isairey/RadarDeteccionObjetos/5_Simulations/array_pattern_heatmap.png

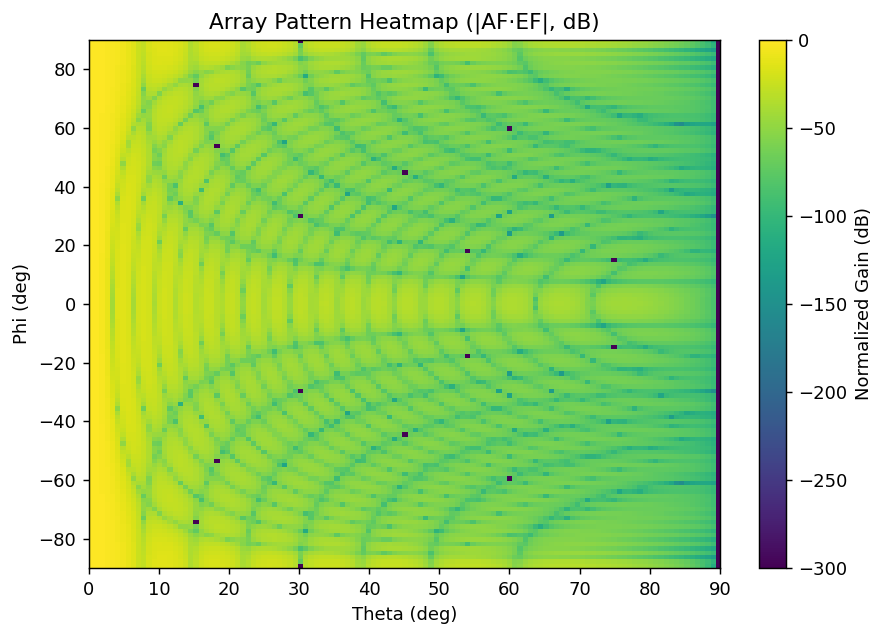
5_Simulations/array_pattern_heatmap.png
