isairey/RadarDeteccionObjetos/5_Simulations/E_plane_cut.png

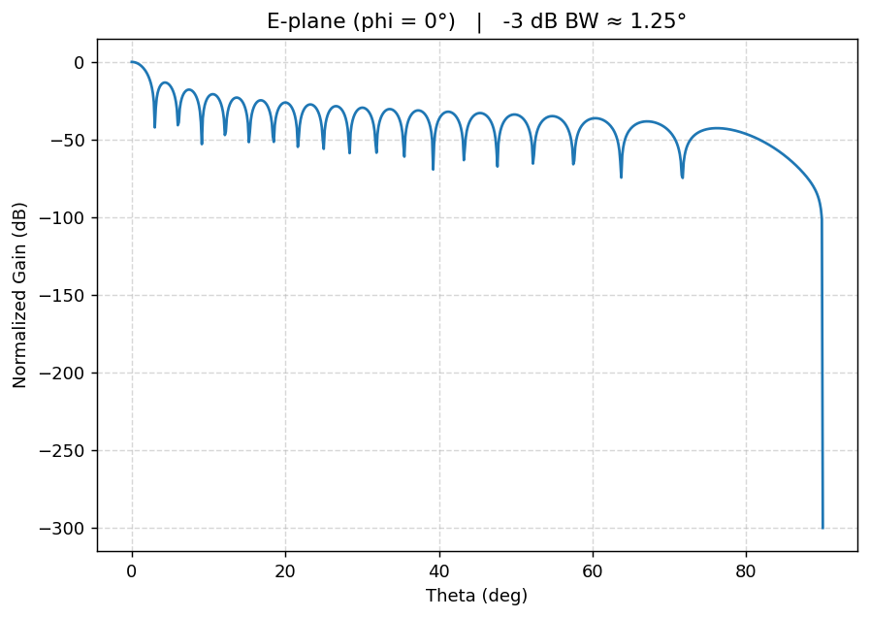
5_Simulations/E_plane_cut.png
