isairey/RadarDeteccionObjetos/5_Simulations/E_plane_Kaiser25dB_like.png

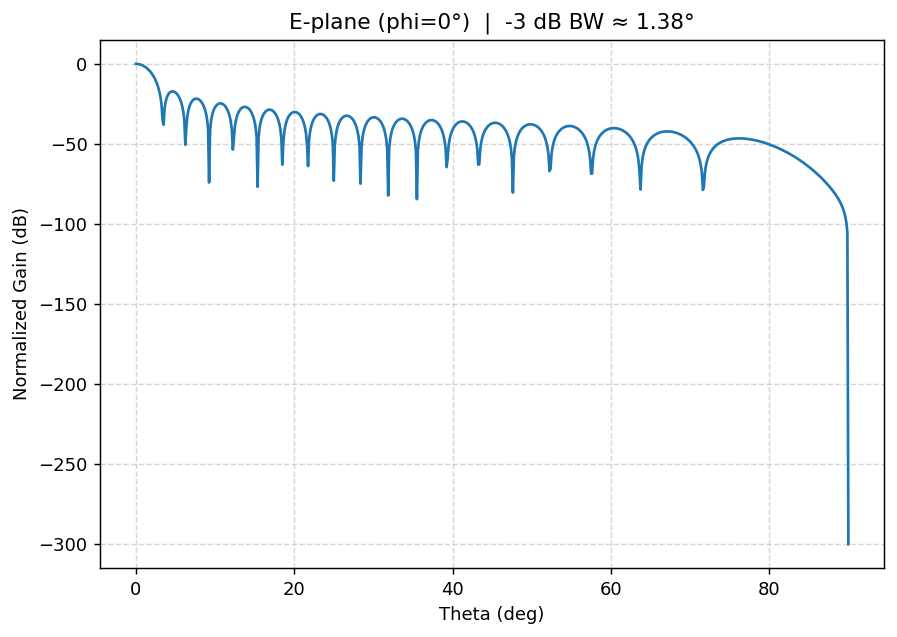
5_Simulations/E_plane_Kaiser25dB_like.png
