isairey/RadarDeteccionObjetos/5_Simulations/H_plane_cut.png

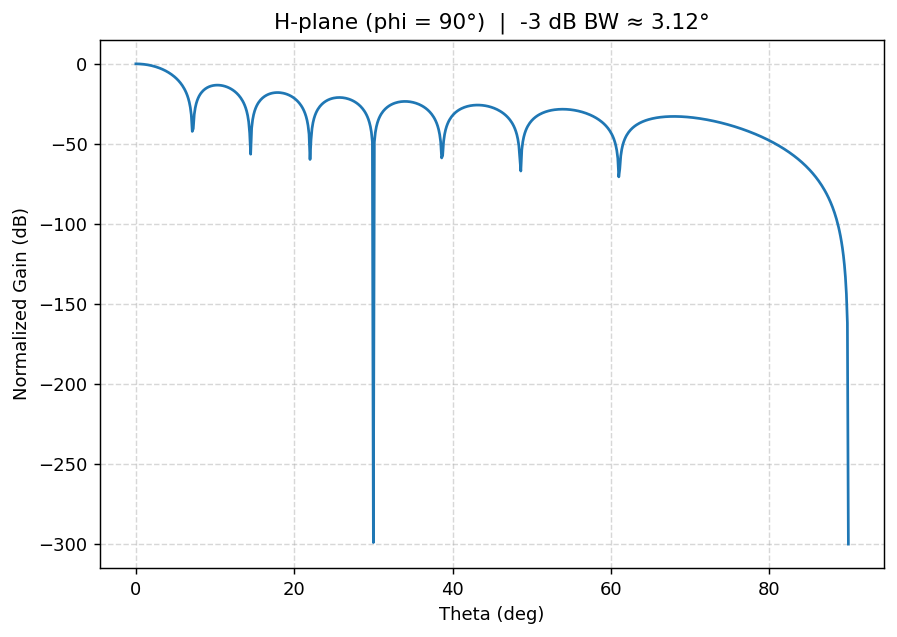
5_Simulations/H_plane_cut.png
