isairey/RadarDeteccionObjetos/8_Utils/AERIS-10_RADAR.png

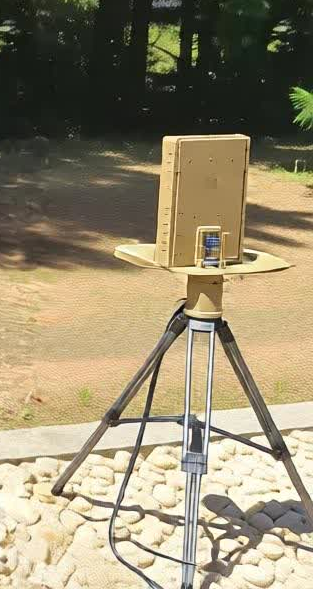
8_Utils/AERIS-10_RADAR.png
