isairey/RadarDeteccionObjetos/8_Utils/b79a6fe3-5abf-473d-b3e2-178e6a9cf4da - Copie.jpg

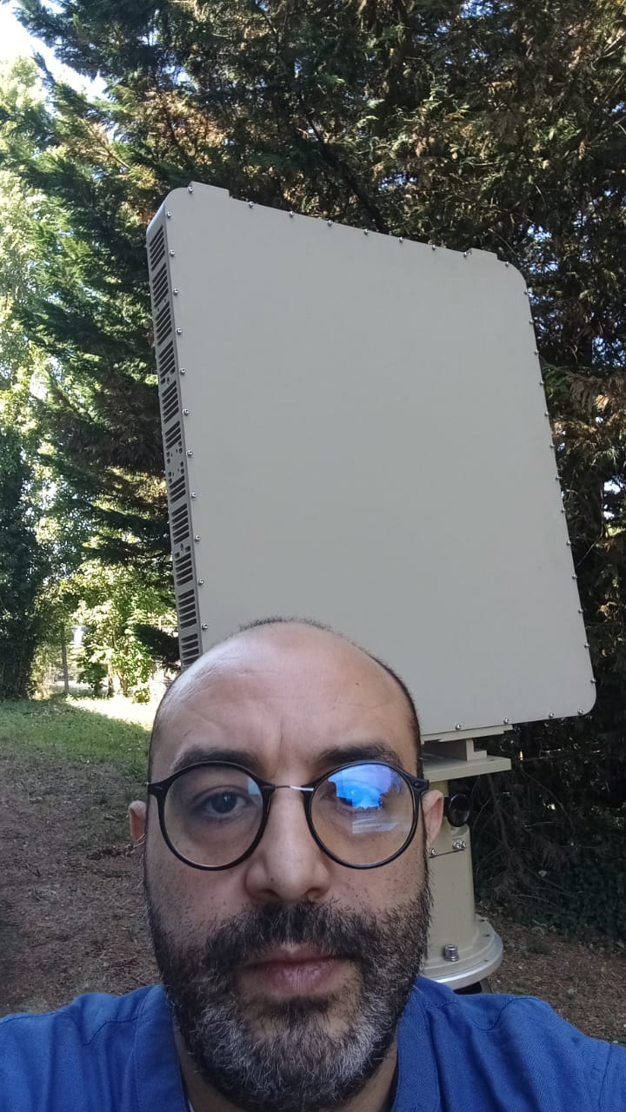
8_Utils/b79a6fe3-5abf-473d-b3e2-178e6a9cf4da - Copie.jpg
