isairey/RadarDeteccionObjetos/8_Utils/Nawfal.png

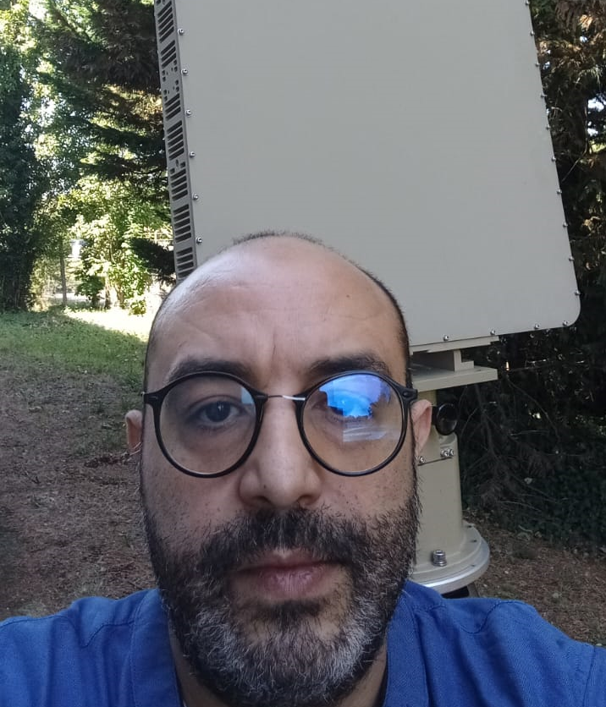
8_Utils/Nawfal.png
