isairey/RadarDeteccionObjetos/8_Utils/PCBWAY.jpg

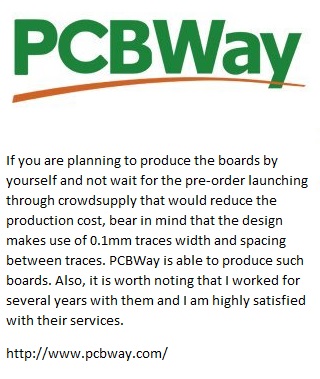
8_Utils/PCBWAY.jpg
