isairey/RadarDeteccionObjetos/3_Power Management/Power Management V6.xlsx

BOARD | COMPONENT | PART NUMBER | N° | VOLTAGE PINS | RATING (V) | CURRENT (mA) | SELECTED VOLTAGE (V) | VOLTAGE RAIL | VOLTAGE RAIL AFTER BRANCHING AND FILTERING | ENABLE V | SEQUENCE
CLOCKS & FREQUENCY SYNTHESIZER BOARD | OCXO | ECOC-2522-100.000-3FC | 1 | VDD | [3,135-3,465] | 1200 | 3.3 | +3V3_XO |  | NO | NO
 |  |  |  | VREF |  |  | 3,3/2 | +3V3_XO |  | NO | NO
 | XO | CCHD-957-100 | 1 | VDD | [3-3,6] | 25 | 3.3 | +3V3_XO |  | NO | NO
 | VCXO | CVHD-950-100.000 | 1 | VDD | [3-3,6] | 25 | 3.3 | +3V3_XO |  | NO | NO
 | CLOCK SYNTHESIZER | AD9523 | 1 | VDD3_REF, VDD3_PLL, VDD3_OUT | 3.3 | 250 | 3.3 | +3V3_CLOCK |  | YES | bring the 1.8 V supplies high and stable prior to or simultaneously with the 3.3 V supplies. It is recommended to hold the RESET pin low while both supply domains settle to ensure that the 3.3 V supplies do not lead the 1.8 V supplies
 |  |  |  | VDD1.8_OUT | 1.8 | 250 | 1.8 | +1V8_CLOCK |  | YES
 | LO | ADF4382 | 2 | V5_VCO | [4,75-5,25] | 200 | 5 | +5V0_LO |  | NO | NO
 |  |  |  | V5_CAL | [4,75-5,25] | 0.3 | 5 | +5V0_LO |  | NO | NO
 |  |  |  | V5_CP | [4,75-5,25] | 70 | 5 | +5V0_LO |  | NO | NO
 |  |  |  | V3V3_1 | [3,15-3,45] | 240 | 3.3 | +3V3_LO_1 |  | NO | NO
 |  |  |  | V3V3_2 | [3,15-3,45] | 340 | 3.3 | +3V3_LO_2 |  | NO | NO
MAIN BOARD | MICROCONTROLLER | STM32F746ZGT7 | 1 | VCC | 3.3 | 130 | 3.3 | +3V3 |  | NO | NO
 | FPGA | XC7A50T-2FTG256 | 1 | VCC0_BANK | 1.8 | 50 | 1.8 | +1V8_FPGA |  | YES
 |  |  |  | VCCO_O | 3.3 | 20 | 3.3 | +3V3_FPGA |  | YES | +1V0_FPGA
 |  |  |  | VCCBAT, VCCADC, VCCAUX | 1.8 | 22 | 1.8 | +1V8_FPGA |  | YES | +1V8_FPGA
 |  |  |  | VCCBRAM, VCCINT | 1 | 30 | 1 | +1V0_FPGA |  | YES | +3V3_FPGA
 |  |  |  | VCCO_BANK x 3 | 3.3 | 200 | 3.3 | +3V3_FPGA |  | YES
 | DAC | AD9708 | 1 | AVDD | [2,7-5,5] | 30 | 3.3 | +3V3_AN | +3V3_AN | NO | NO
 |  |  |  | DVDD | [2,7-5,5] | 20 | 3.3 | +3V3_FPGA |  | NO | NO
 | Mixer | LTC5552 | 2 | VCC | [3,0-3,6] | 150 | 3.3 | +3V3_AN | +3V3_AN1_F |+3V3_AN2_F | NO | NO
 | RF SWITCH | M3SWA2-34DR+ | 17 | VDD | [3,3-3,6] | 2.9 | 3.4 | +3V4 |  | NO | NO
 |  |  |  | VEE | [-3,6--3,3] | 1.8 | -3.4 | -3V4 |  | NO | NO
 | OPAMP | AD8352 | 2 | VCC | [3-5,5] | 200 | 5 | +5V0_0 |  | NO | NO
 | ADC | AD9484 | 1 | AVDD | [1,75-1,9] | 300 | 1.8 | +1V8_CLOCK | +1V8_CLOCK_F | NO | NO
 |  |  |  | DRVDD | [1,75-1,9] | 100 | 1.8 | +1V8_FPGA |  | NO | NO
 | USB 3 | FT601 | 1 | VCCIO, VPLL, VPHY, VREGIN | 3.3 | 230 | 3.3 | +3V3_FPGA |  | NO | NO
 |  |  |  | VREGOUT --> VCORE | 1.8 |  | 1.8 | +1V8_FT |  | NO | NO
 | PHASER | ADAR1000 | 4 | AVDD1 | [-5--4,75] | 60 | -5 | -5V0_ADAR12 |-5V0_ADAR34 |  | YES | TX Power_up | RX Power-up
 |  |  |  | AVDD3 | [3,1-3,5] | 700 | 3.3 | +3V3_ADAR12 | +3V3_ADAR34 | +3V3_ADAR1_F | +3V3_ADAR2_F | +3V3_ADAR3_F | +3V3_ADAR4_F |  | It is recommended to power up the AVDD3 pins (3.3 V) before or at the same time as the AVDD1 pin (−5 V)
 |  |  |  |  |  |  |  |  |  |  | 1. Connect all GND pins to ground. | 1. Connect all GND pins to ground.
 | RF FRONT END | ADTR1107 | 16 |  |  |  |  |  |  |  | 2. Set the VDD_SW pin to 3.3 V. | 2. Set the VDD_SW pin to 3.3 V.
 |  |  |  |  |  |  |  |  |  |  | 3. Set the VSS_SW pin to −3.3 V. | 3. Set the VSS_SW pin to −3.3 V.
 |  |  |  |  |  |  |  |  |  |  | 4. Set the CTRL_SW pin to 0 V. | 4. Set the CTRL_SW pin to 3.3 V.
 |  |  |  | VDD_LNA | 3.3 | 80 | 3.3 | +3V3_ADTR |  |  | 5. Set the VGG_LNA pin to 0 V. | 5. Set the VGG_PA pin to −1.75 V.
 |  |  |  | VGG_LNA | ADAR1000 CON |  |  |  |  |  | 6. Set the VDD_LNA pin to 0 V. | 6. Set the VDD_PA pin to 0 V.
 |  |  |  | VSS_SW | [-3,6-0,3] | 0.12 | -3.3 | -3V3_SW |  |  | 7. Set the VGG_PA pin to −1.75 V. | 7. Set the VGG_LNA pin to 0 V.
 |  |  |  | VDD_SW | [-0,3-3,6] | 0.014 | 3.3 | +3V3_VDD_SW |  |  | 8. Set the VDD_PA pin to 5 V. | 8. Set the VDD_LNA pin to 3.3 V.
 |  |  |  | VGG_PA | ADAR1000 CON |  |  |  |  |  | 9. Increase the VGG_PA voltage to achieve the desired IDQ_PA. | 9. Apply the RF signal to the ANT pin.
 |  |  |  | VDD_PA | [3.3-5,5] | 250 | 5 | +5V0_PA_1 | +5V0_PA_2 | +5V0_PA_3 |  |  | 10. Apply the RF signal to the TX_IN pin.
 |  |  |  |  |  |  |  |  |  |  | TX Power_down | RX Power_down
 |  |  |  |  |  |  |  |  |  |  | 1. Turn off the RF signal. | 1. Turn off the RF signal.
 |  |  |  |  |  |  |  |  |  |  | 2. Decrease the VGG_PA voltage to −1.75 V. | 2. Set the VDD_LNA pin to 0 V.
 |  |  |  |  |  |  |  |  |  |  | 3. Set the VDD_PA pin to 0 V. | 3. Set the CTRL_SW pin to 0 V.
 |  |  |  |  |  |  |  |  |  |  | 4. Set the VSS_SW pin to 0 V. | 4. Set the VSS_SW pin to 0 V.
 |  |  |  |  |  |  |  |  |  |  | 5. Set the VDD_SW pin to 0 V. | 5. Set the VDD_SW pin to 0 V.
 | IMU | GY-85 | 1 | Vcc | 3.3 | 10 | 3.3 | +3V3 |  | NO | NO
 | Barometer | BMP180 | 1 | Vcc | 3.3 | 1 | 3.3 | +3V3 |  | NO
 | GPS | NEO-6M | 1 | Vcc | 3.3 | 50 | 3.3 | +3V3 |  | NO | NO
 | Temperature Sensor | TMP37 | 1 | Vs | [2,7-5,5] | 1 | 3.3 | +3V3_AN | +3V3_AN4_F | NO | NO
 | DAC PA | DAC5578 | 2 | Vcc | [2,7-5] | 1 | 3.3 | +3V3_AN | +3V3_AN3_F | NO | NO
 | OPAMP PA | OPA4703NA/250 | 2 | V+ | [2-6] | 50 | 5.5 | +5V5_PA |  | YES
 |  |  |  | V- | [-6--2] | 50 | -5.5 | -5V5_PA |  | YES
 | ADC PA & T°C Sensor | ADS7830 | 3 | VDD | [2,5-5] | 2 | 3.3 | +3V3_AN | +3V3_AN4_F | NO | NO
 |  |  |  | VREF | [2,5-5] | 1 | 3.3 | +3V3 |  | NO | NO
 | CURRENT SENSOR PA | INA241A3 | 16 | VDD | [2,7-20] | 6 | 3.3 | +3V3_AN | +3V3_AN5_F | +3V3_AN6_F | NO | NO
MICROWAVE POWER AMPLIFIER BOARD | RF POWER AMPLIFIER | QPA2962 | 16 |  |  |  |  |  |  |  | Bias-up Procedure | Bias-Down Procedure
 |  |  |  |  |  |  |  |  |  |  | Set ID limit to 2840 mA, IG limit to 10 mA | Turn off RF signal
 |  |  |  | VD | [18-22] | 2000 | 22 | +22V0 |  | YES | Set VG to −4.0 V | Reduce VG to −4.0 V. Ensure IDQ ~ 0 mA
 |  |  |  | VG | [-4--1,2] | 10 |  | DAC |  | YES | Set VD +22 V | Set VD to 0 V
 |  |  |  |  |  |  |  |  |  |  | Adjust VG more positive until IDQ = 1680 mA | Turn off VD supply
 |  |  |  |  |  |  |  |  |  |  | Apply RF signal | Turn off VG supply
MISCELLANEOUS | STEPPER MOTOR DRIVER | TBS6600 | 1 | VDD | [9-42] | 4000 | 20 |  |  | NO
 | COOLING SYSTEM |  | 1 |  |  |  |  |  |  | YES | Apply when temperature reaches a threshold (Relay)
