isairey/RadarDeteccionObjetos/5_Simulations/Fencing/via_fence_setup_pitch.png

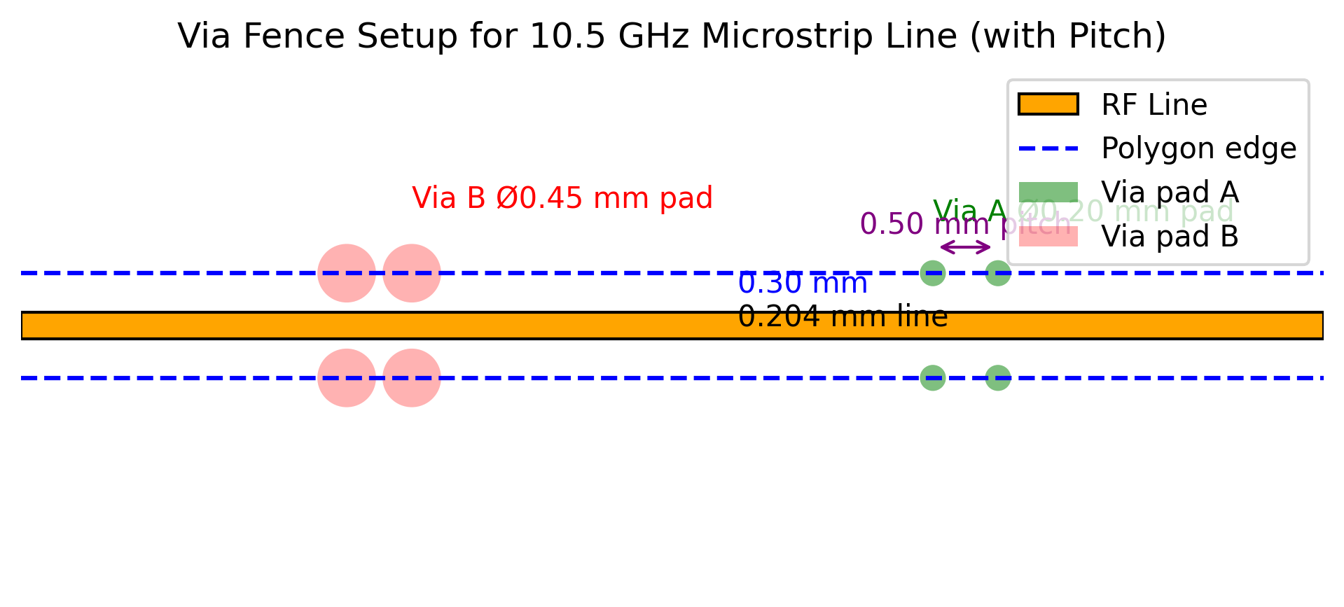
5_Simulations/Fencing/via_fence_setup_pitch.png
