isairey/RadarDeteccionObjetos/5_Simulations/Fencing/via_fence_setup_pitch_offset.png

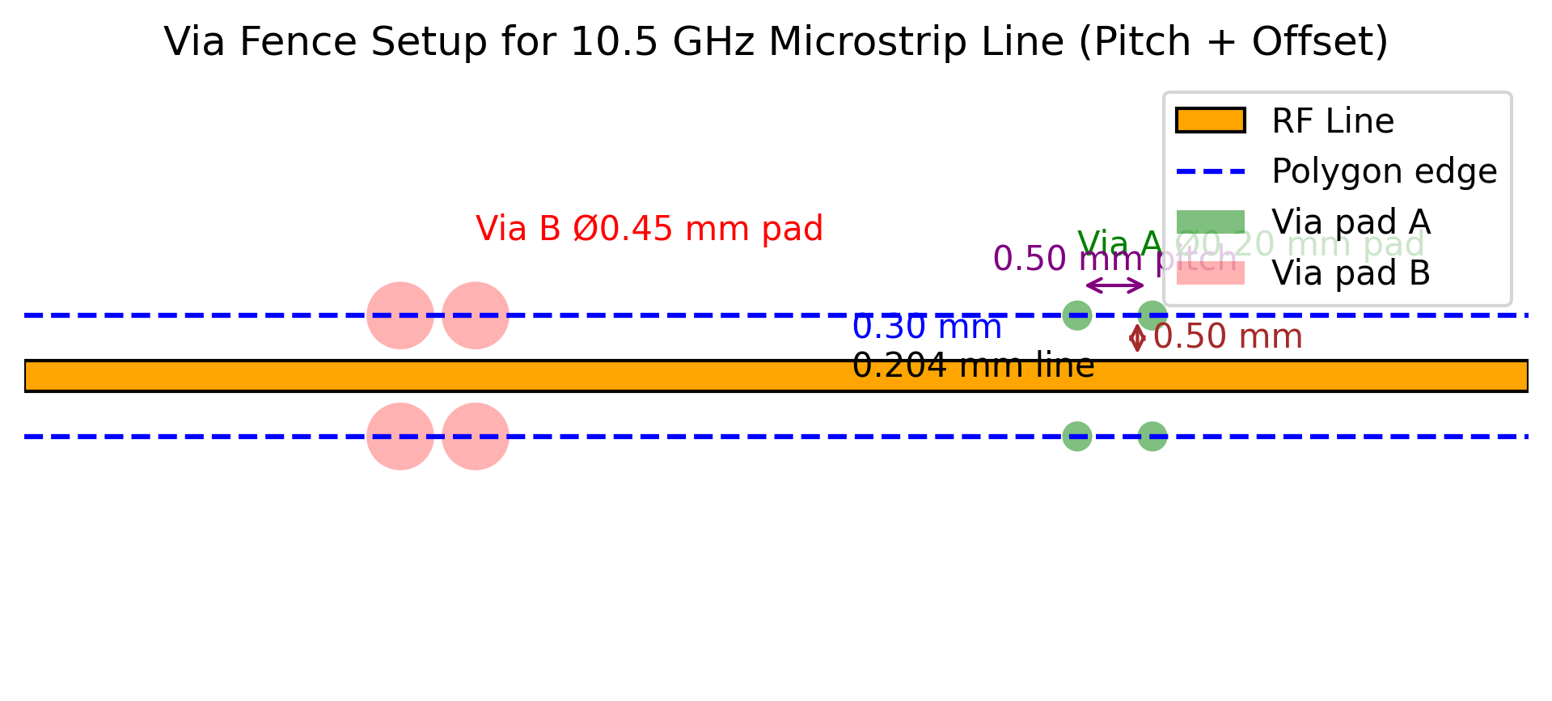
5_Simulations/Fencing/via_fence_setup_pitch_offset.png
