isairey/RadarDeteccionObjetos/9_Firmware/9_1_Microcontroller/9_1_1_C_Cpp_Libraries/stm32_delay.h

#ifndef _STM32_DELAY_H_
#define _STM32_DELAY_H_

#include "stm32f7xx_hal.h"

/* prototypes for compatibility */
void no_os_udelay(uint32_t usec);
void no_os_mdelay(uint32_t msec);

#endif /* _STM32_DELAY_H_ */
